AleDedor/Discrete_OpAmp/LTSpice/MOS_Modeling.asc

I3: current; 1m
I4: current; 1
M1: pmos; BSD223P
M2: nmos; BSD235N
Q3: pnp; BC857B
Q4: npn; BC847B
V1: voltage; 3
V2: voltage; 5
V3: voltage; 3
V4: voltage; {X}
V5: voltage; 5
V6: voltage; 5
Named nets: 0
.MODEL BSD235N VDMOS( Vto=1 Kp=2.40 W=26u L=100u Lambda=0.02 BV=20 Cgs=46p Cgdmin=3.2p Cgdmax=3.2p)
.dc V3 0 3 0.1
.MODEL BSD223P VDMOS(pchan  Vto=-0.9 Kp=0.51 W=82u L=100u Lambda=0.01 BV=-20 Cgs=28p Cgdmin=17p Cgdmax=17p)
.MODEL FDG6301N VDMOS( Vto=0.85 Kp=0.124 W=1.31u L=1u Lambda=0.012 BV=25 Cgs=8.2p Cgdmin=1.3p Cgdmax=1.3p)
.MODEL FDG6302P VDMOS(pchan  Vto=-0.9 Kp=0.0695 W=1.17u L=1u Lambda=0.01 BV=-25 Cgs=10.5p Cgdmin=1.5p Cgdmax=1.5p)
.step param X 2.2 3 0.3
.MODEL FDG6335 VDMOS( Vto=0.95 Kp=3.24 W=90u L=100u Lambda=0.012 BV=20 Cgs=97p Cgdmin=16p Cgdmax=16p)
.MODEL FDG6306 VDMOS(pchan  Vto=-1.2 Kp=2.49 W=68u L=100u Lambda=0.01 BV=-20 Cgs=105p Cgdmin=9p Cgdmax=9p)
