AleDedor/Discrete_OpAmp/LTSpice/OpAmp_discreto_4.asc

-Vss: voltage; 5
C1: cap; 1n
M1: nmos; BSD235N
M2: nmos; BSD235N
Q1: npn; BC847B
Q2: pnp; BC857B
Q3: npn; BC847B
Q4: pnp; BC857B
Q6: pnp; BC857B
Q9: npn; BC847B
Q10: npn; BC847B
Q11: npn; BC847B
Q13: npn; BC847B
Q14: npn; BC847B
Q15: pnp; BC857B
Q16: pnp; BC857B
Q19: pnp; BC857B
Q20: pnp; BC857B
R1: res; 10k
R2: res; 1k
R6: res; 10k
V1: voltage; SINE(0 1u 100); AC 1u
Vdd: voltage; 5
Named nets: 0, VDD, -VSS, Vo2, VOUT, Vo1, V+, V-, VB9A, VB8A
;ac dec 100 1 100meg
.MODEL BSD235N VDMOS( Vto=1 Kp=2.40 W=26u L=100u Lambda=0.02 BV=20 Cgs=46p Cgdmin=3.2p Cgdmax=3.2p)
.MODEL BSD223P VDMOS(pchan  Vto=-0.9 Kp=0.51 W=82u L=100u Lambda=0.01 BV=-20 Cgs=28p Cgdmin=17p Cgdmax=17p)
.MODEL FDG6335 VDMOS( Vto=0.95 Kp=0.001 W=90u L=100u Lambda=0.012 BV=20 Cgs=97p Cgdmin=16p Cgdmax=16p)
.tran 20m
;step param R 10 100 10
